behind-the-moon/abc-lcd/src/tools.h

/*********************************************************************************
* File Name     : tools.h
* Created By    : Svetlana Linuxenko
* Creation Date : [2019-09-21 13:33]
* Last Modified : [2019-09-21 19:33]
* Description   :  
**********************************************************************************/

#ifndef _ABC_TOOLS_H
#define _ABC_TOOLS_H

void float_to_str (char *s, float val);

#endif
